AlessiaRinaldi/2D-plotter-manipulator/readme/photo3.jpg

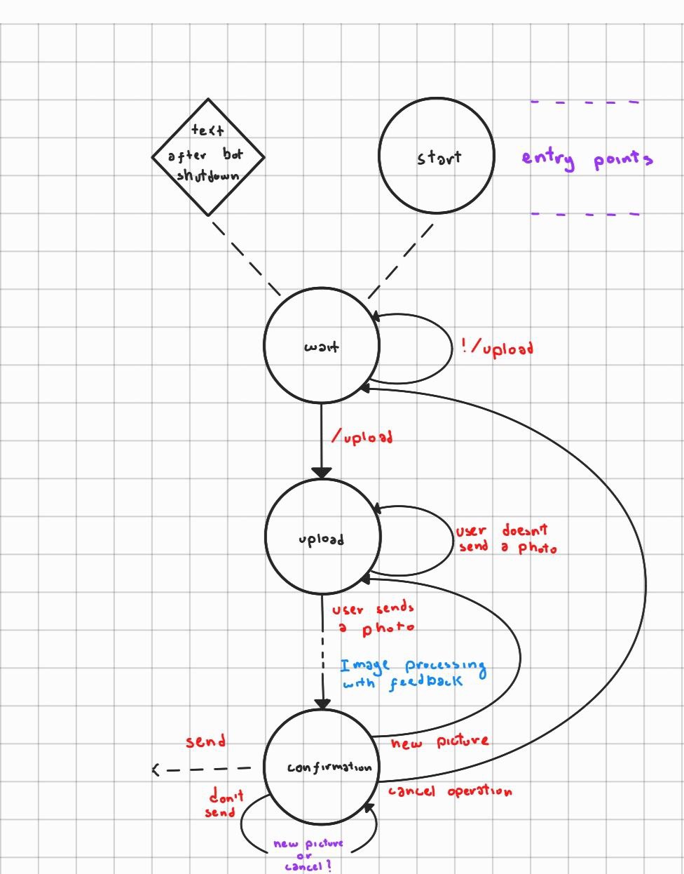
readme/photo3.jpg
