AlessiaRinaldi/2D-plotter-manipulator/readme/pullup1.png

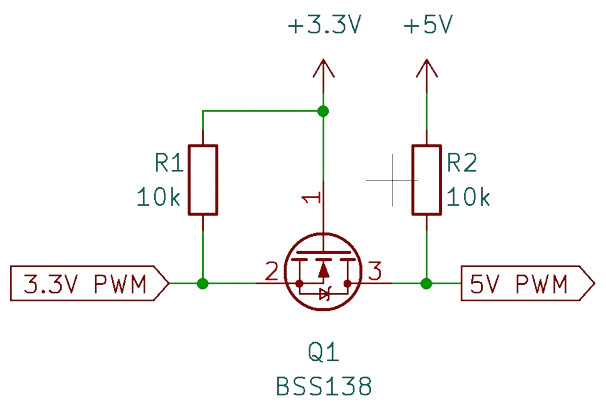
readme/pullup1.png
