AlessiaRinaldi/2D-plotter-manipulator/pwm_lifter_simulation.asc

R1: res; 10k
R2: res; 10k
U1: bss138lt1
V1: voltage; 3.3
V2: voltage; 5
V3: voltage; PULSE(0 3.3 0 0 0 0.0001 0.00015 100)
Named nets: 0, 5V-PWM, 3.3V-PWM
.tran 0.1
