AlessiaRinaldi/2D-plotter-manipulator/MSP-codes/src/communication.h

/*
This file includes the headers for the serial communication between Raspberry and MSP432
*/

#ifndef __COMMUNICATION_H__
#define __COMMUNICATION_H__

#include "msp.h"
#include <driverlib.h>

bool get_vector;

typedef struct pos_t{
    uint8_t x;
    uint8_t y;
    bool pen;
} pos_t;

void init_UART();

void UART_get_data(pos_t *pos);

void UART_get_vectors(void);

#endif
